salmec/Synteremino_v1.0/07 Push Button X6.stl

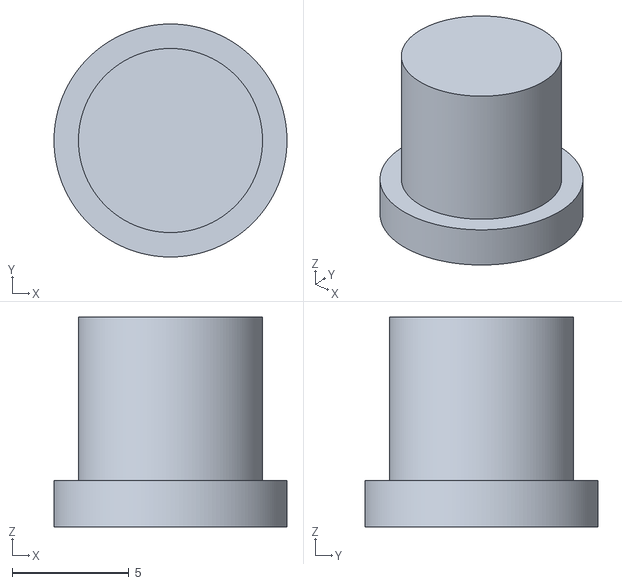
[picture p16: CAD file, 2025-06-30]
07 Push Button X6.stl
10.00 x 10.0 x 9.00
