salmec/Synteremino_v1.0/08 Power plug stop.stl

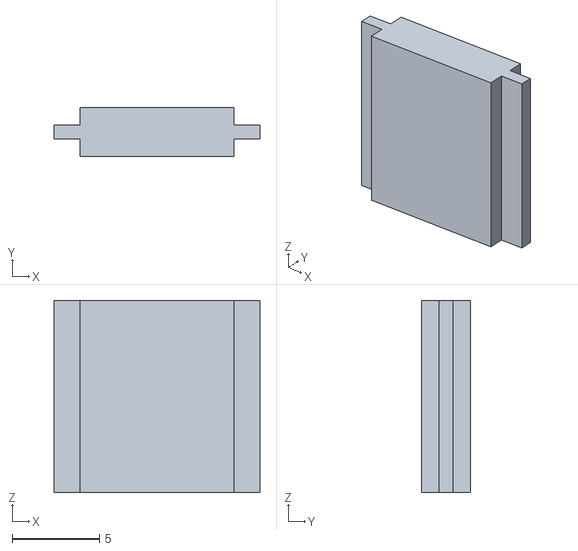
[picture p17: CAD file, 2025-06-30]
08 Power plug stop.stl
11.8 x 2.80 x 11.0
